toor0001/PoolGuard/images/IMG_5329.png

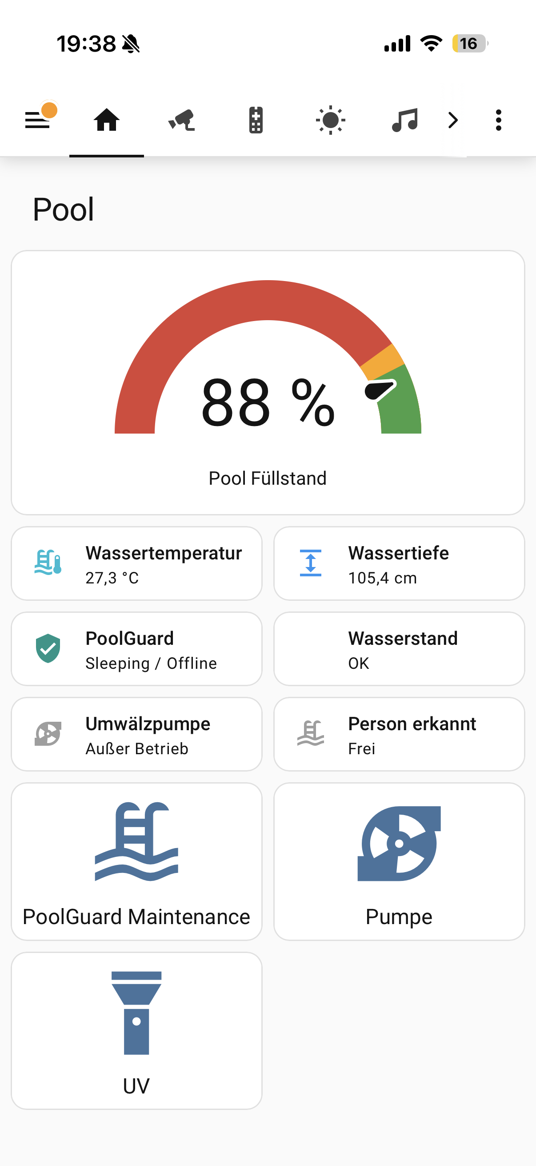
images/IMG_5329.png
